vansh2966/keyboard-bubble-/PCB/LEDS.kicad_sch

## KiCad design PCB/LEDS.kicad_sch (2026-06-02)

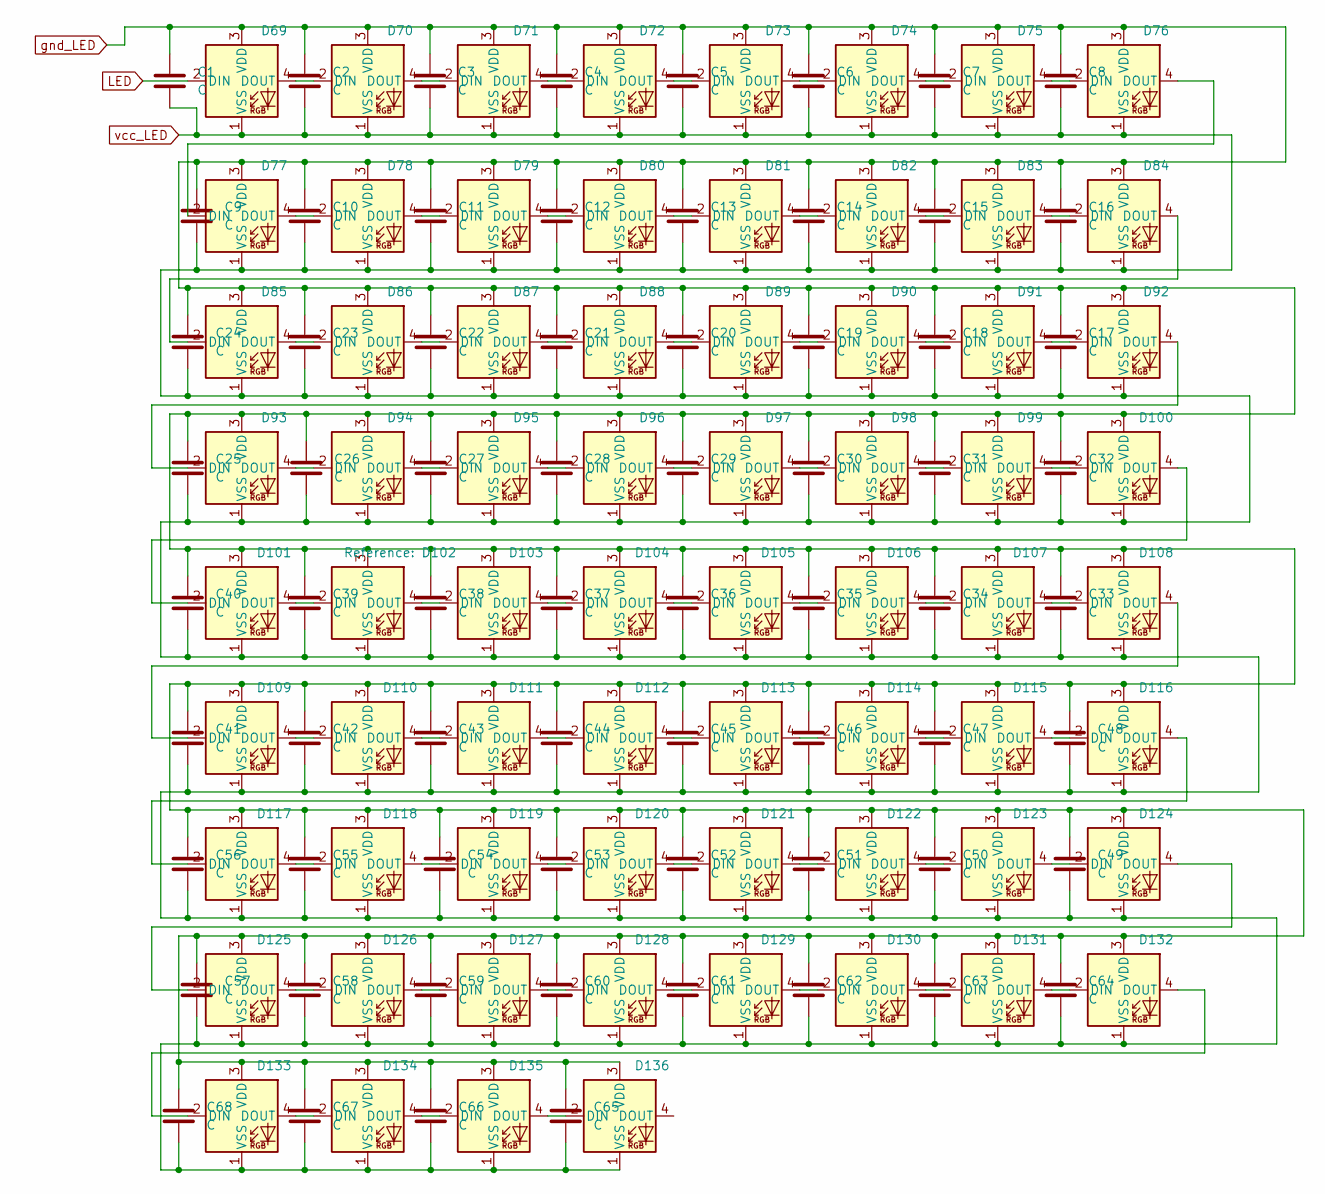
[picture p5: schematic LEDS.kicad_sch]

Parts:
C1, C2, C3, C4, C5, C6, C7, C8, C9, C10, C11, C12, C13, C14, C15, C16, C17, C18, C19, C20, C21, C22, C23, C24, C25, C26, C27, C28, C29, C30, C31, C32, C33, C34, C35, C36, C37, C38, C39, C40, C41, C42, C43, C44, C45, C46, C47, C48, C49, C50, C51, C52, C53, C54, C55, C56, C57, C58, C59, C60, C61, C62, C63, C64, C65, C66, C67, C68: C; C_0402_1005Metric
D69, D70, D71, D72, D73, D74, D75, D76, D77, D78, D79, D80, D81, D82, D83, D84, D85, D86, D87, D88, D89, D90, D91, D92, D93, D94, D95, D96, D97, D98, D99, D100, D101, D102, D103, D104, D105, D106, D107, D108, D109, D110, D111, D112, D113, D114, D115, D116, D117, D118, D119, D120, D121, D122, D123, D124, D125, D126, D127, D128, D129, D130, D131, D132, D133, D134, D135, D136: SK6812MINI-E; LED_SK6812MINI-E_3.2x2.8mm_P1.5mm_ReverseMount

Connections:
LED: D69.2 (DIN)
unnamed: D69.4 (DOUT), D70.2 (DIN)
unnamed: D70.4 (DOUT), D71.2 (DIN)
unnamed: D71.4 (DOUT), D72.2 (DIN)
unnamed: D72.4 (DOUT), D73.2 (DIN)
unnamed: D73.4 (DOUT), D74.2 (DIN)
unnamed: D74.4 (DOUT), D75.2 (DIN)
unnamed: D75.4 (DOUT), D76.2 (DIN)
unnamed: D76.4 (DOUT), D77.2 (DIN)
unnamed: D77.4 (DOUT), D78.2 (DIN)
unnamed: D78.4 (DOUT), D79.2 (DIN)
unnamed: D79.4 (DOUT), D80.2 (DIN)
unnamed: D80.4 (DOUT), D81.2 (DIN)
unnamed: D81.4 (DOUT), D82.2 (DIN)
unnamed: D82.4 (DOUT), D83.2 (DIN)
unnamed: D83.4 (DOUT), D84.2 (DIN)
unnamed: D84.4 (DOUT), D85.2 (DIN)
unnamed: D85.4 (DOUT), D86.2 (DIN)
unnamed: D86.4 (DOUT), D87.2 (DIN)
unnamed: D87.4 (DOUT), D88.2 (DIN)
unnamed: D88.4 (DOUT), D89.2 (DIN)
unnamed: D89.4 (DOUT), D90.2 (DIN)
unnamed: D90.4 (DOUT), D91.2 (DIN)
unnamed: D91.4 (DOUT), D92.2 (DIN)
unnamed: D92.4 (DOUT), D93.2 (DIN)
unnamed: D93.4 (DOUT), D94.2 (DIN)
unnamed: D94.4 (DOUT), D95.2 (DIN)
unnamed: D95.4 (DOUT), D96.2 (DIN)
unnamed: D96.4 (DOUT), D97.2 (DIN)
unnamed: D97.4 (DOUT), D98.2 (DIN)
unnamed: D98.4 (DOUT), D99.2 (DIN)
unnamed: D99.4 (DOUT), D100.2 (DIN)
unnamed: D100.4 (DOUT), D101.2 (DIN)
unnamed: D101.4 (DOUT), D102.2 (DIN)
unnamed: D102.4 (DOUT), D103.2 (DIN)
unnamed: D103.4 (DOUT), D104.2 (DIN)
unnamed: D104.4 (DOUT), D105.2 (DIN)
unnamed: D105.4 (DOUT), D106.2 (DIN)
unnamed: D106.4 (DOUT), D107.2 (DIN)
unnamed: D107.4 (DOUT), D108.2 (DIN)
unnamed: D108.4 (DOUT), D109.2 (DIN)
unnamed: D109.4 (DOUT), D110.2 (DIN)
unnamed: D110.4 (DOUT), D111.2 (DIN)
unnamed: D111.4 (DOUT), D112.2 (DIN)
unnamed: D112.4 (DOUT), D113.2 (DIN)
unnamed: D113.4 (DOUT), D114.2 (DIN)
unnamed: D114.4 (DOUT), D115.2 (DIN)
unnamed: D115.4 (DOUT), D116.2 (DIN)
unnamed: D116.4 (DOUT), D117.2 (DIN)
unnamed: D117.4 (DOUT), D118.2 (DIN)
unnamed: D118.4 (DOUT), D119.2 (DIN)
unnamed: D119.4 (DOUT), D120.2 (DIN)
unnamed: D120.4 (DOUT), D121.2 (DIN)
unnamed: D121.4 (DOUT), D122.2 (DIN)
unnamed: D122.4 (DOUT), D123.2 (DIN)
unnamed: D123.4 (DOUT), D124.2 (DIN)
unnamed: D124.4 (DOUT), D125.2 (DIN)
unnamed: D125.4 (DOUT), D126.2 (DIN)
unnamed: D126.4 (DOUT), D127.2 (DIN)
unnamed: D127.4 (DOUT), D128.2 (DIN)
unnamed: D128.4 (DOUT), D129.2 (DIN)
unnamed: D129.4 (DOUT), D130.2 (DIN)
unnamed: D130.4 (DOUT), D131.2 (DIN)
unnamed: D131.4 (DOUT), D132.2 (DIN)
unnamed: D132.4 (DOUT), D133.2 (DIN)
unnamed: D133.4 (DOUT), D134.2 (DIN)
unnamed: D134.4 (DOUT), D135.2 (DIN)
unnamed: D135.4 (DOUT), D136.2 (DIN)
gnd_LED: C1.1, C2.1, C3.1, C4.1, C5.1, C6.1, C7.1, C8.1, C9.1, C10.1, C11.1, C12.1, C13.1, C14.1, C15.1, C16.1, C17.1, C18.1, C19.1, C20.1, C21.1, C22.1, C23.1, C24.1, C25.1, C26.1, C27.1, C28.1, C29.1, C30.1, C31.1, C32.1, C33.1, C34.1, C35.1, C36.1, C37.1, C38.1, C39.1, C40.1, C41.1, C42.1, C43.1, C44.1, C45.1, C46.1, C47.1, C48.1, C49.1, C50.1, C51.1, C52.1, C53.1, C54.1, C55.1, C56.1, C57.1, C58.1, C59.1, C60.1, C61.1, C62.1, C63.1, C64.1, C65.1, C66.1, C67.1, C68.1, D69.3 (VDD), D70.3 (VDD), D71.3 (VDD), D72.3 (VDD), D73.3 (VDD), D74.3 (VDD), D75.3 (VDD), D76.3 (VDD), D77.3 (VDD), D78.3 (VDD), D79.3 (VDD), D80.3 (VDD), D81.3 (VDD), D82.3 (VDD), D83.3 (VDD), D84.3 (VDD), D85.3 (VDD), D86.3 (VDD), D87.3 (VDD), D88.3 (VDD), D89.3 (VDD), D90.3 (VDD), D91.3 (VDD), D92.3 (VDD), D93.3 (VDD), D94.3 (VDD), D95.3 (VDD), D96.3 (VDD), D97.3 (VDD), D98.3 (VDD), D99.3 (VDD), D100.3 (VDD), D101.3 (VDD), D102.3 (VDD), D103.3 (VDD), D104.3 (VDD), D105.3 (VDD), D106.3 (VDD), D107.3 (VDD), D108.3 (VDD), D109.3 (VDD), D110.3 (VDD), D111.3 (VDD), D112.3 (VDD), D113.3 (VDD), D114.3 (VDD), D115.3 (VDD), D116.3 (VDD), D117.3 (VDD), D118.3 (VDD), D119.3 (VDD), D120.3 (VDD), D121.3 (VDD), D122.3 (VDD), D123.3 (VDD), D124.3 (VDD), D125.3 (VDD), D126.3 (VDD), D127.3 (VDD), D128.3 (VDD), D129.3 (VDD), D130.3 (VDD), D131.3 (VDD), D132.3 (VDD), D133.3 (VDD), D134.3 (VDD), D135.3 (VDD), D136.3 (VDD)
vcc_LED: C1.2, C2.2, C3.2, C4.2, C5.2, C6.2, C7.2, C8.2, C9.2, C10.2, C11.2, C12.2, C13.2, C14.2, C15.2, C16.2, C17.2, C18.2, C19.2, C20.2, C21.2, C22.2, C23.2, C24.2, C25.2, C26.2, C27.2, C28.2, C29.2, C30.2, C31.2, C32.2, C33.2, C34.2, C35.2, C36.2, C37.2, C38.2, C39.2, C40.2, C41.2, C42.2, C43.2, C44.2, C45.2, C46.2, C47.2, C48.2, C49.2, C50.2, C51.2, C52.2, C53.2, C54.2, C55.2, C56.2, C57.2, C58.2, C59.2, C60.2, C61.2, C62.2, C63.2, C64.2, C65.2, C66.2, C67.2, C68.2, D69.1 (VSS), D70.1 (VSS), D71.1 (VSS), D72.1 (VSS), D73.1 (VSS), D74.1 (VSS), D75.1 (VSS), D76.1 (VSS), D77.1 (VSS), D78.1 (VSS), D79.1 (VSS), D80.1 (VSS), D81.1 (VSS), D82.1 (VSS), D83.1 (VSS), D84.1 (VSS), D85.1 (VSS), D86.1 (VSS), D87.1 (VSS), D88.1 (VSS), D89.1 (VSS), D90.1 (VSS), D91.1 (VSS), D92.1 (VSS), D93.1 (VSS), D94.1 (VSS), D95.1 (VSS), D96.1 (VSS), D97.1 (VSS), D98.1 (VSS), D99.1 (VSS), D100.1 (VSS), D101.1 (VSS), D102.1 (VSS), D103.1 (VSS), D104.1 (VSS), D105.1 (VSS), D106.1 (VSS), D107.1 (VSS), D108.1 (VSS), D109.1 (VSS), D110.1 (VSS), D111.1 (VSS), D112.1 (VSS), D113.1 (VSS), D114.1 (VSS), D115.1 (VSS), D116.1 (VSS), D117.1 (VSS), D118.1 (VSS), D119.1 (VSS), D120.1 (VSS), D121.1 (VSS), D122.1 (VSS), D123.1 (VSS), D124.1 (VSS), D125.1 (VSS), D126.1 (VSS), D127.1 (VSS), D128.1 (VSS), D129.1 (VSS), D130.1 (VSS), D131.1 (VSS), D132.1 (VSS), D133.1 (VSS), D134.1 (VSS), D135.1 (VSS), D136.1 (VSS)
